Predko/ControlElectroEngineAttiny13/Schema_V1.jpg

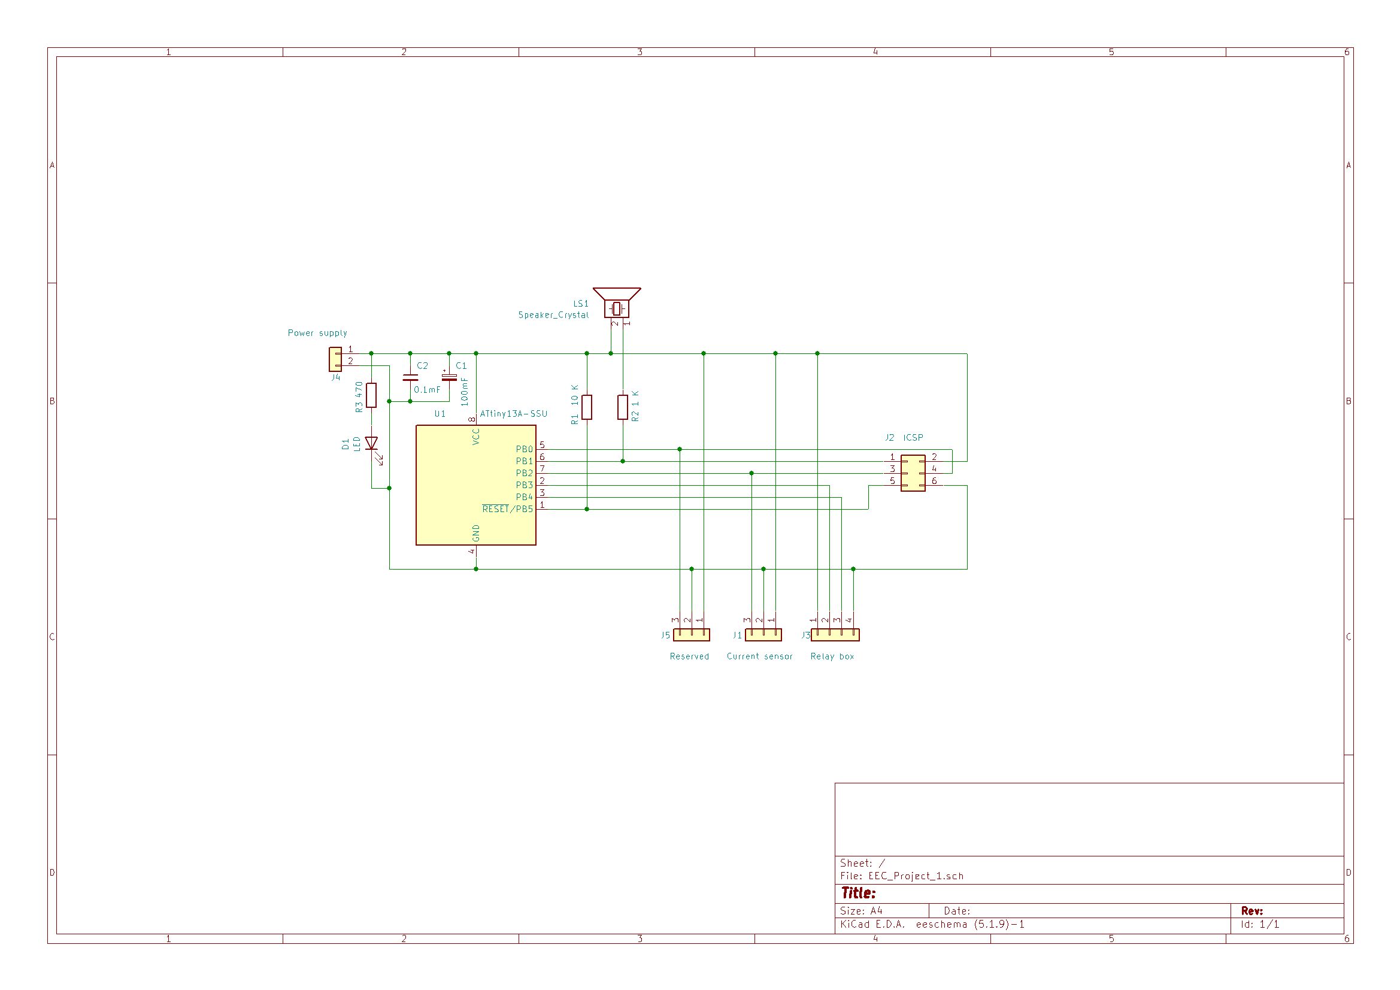
Schema_V1.jpg
