Predko/ControlElectroEngineAttiny13/AnalogIO_1_2Mhz.cpp

//
// NO WARRANTEE OR GUARANTEES!
// Written by Victor Predko 
// You are free to use, redistribute and modify
// 
// 
// 1.2 MHz, built in resonator
// 
//
// Created: 25.12.2020 13:17:20
//  Author: Predko Victor
// 
// ATMEL ATTINY13
//                            
//                                              	 +-\/-+
//	   					(PCINT5/RESET/ADC0/dW) PB5  1|    |8  Vcc
//	Power supply relay -    (PCINT3/CLKI/ADC3) PB3  2|    |7  PB2 (SCK/ADC1/T0/PCINT2) 				- Current sensor pin
//	Reserved	       -    	 (PCINT4/ADC2) PB4  3|    |6  PB1 PWM (MISO/AIN1/OC0B/INT0/PCINT1) 	- Tone port
//                                  		   GND  4|    |5  PB0 PWM (MOSI/AIN0/OC0A/PCINT0)		- Start relay
//                                             		 +----+

#include <avr/io.h>

#include "AnalogIO_1_2Mhz.h"


void Adc_Setup (void)
{
	// Set the ADC input to PB2/ADC1, left adjust result, Vin references
	ADMUX = (1 << MUX0) | (1 << ADLAR); // & ~(1 << REFS0)

	// Set the prescaler to clock_CPU/16 = 75 kHz & enable ADC
	ADCSRA = (1 << ADPS2) | (0 << ADPS1) | (0 << ADPS0) | (1 << ADEN);

	// Disable digital pin PB2
	//DIDR0 |= (1 << ADC1D);
}

uint8_t Adc_Read (void)
{
	// Start the conversion
	ADCSRA |= (1 << ADSC);

	// Wait for it to finish
	while (ADCSRA & (1 << ADSC));

	return ADCH;
}


void Pwm_Setup (uint8_t pinBit)
{
	DDRB |= pinBit;
 
    // Set to 'Fast PWM' mode
    TCCR0A |= (1 << WGM01) | (1 << WGM00);
 
    // Clear OC0A output on compare match, upwards counting. (PB0)
    TCCR0A |= (1 << COM0A1);

	TCCR0B = (1 << CS01);

	// Начальное значение счётчика
	TCNT0 = 0;

	OCR0A = 0;

}
 
void Pwm_Write (uint8_t val)
{
    OCR0A = val;
}
